redaphid/waveshare-round-stand/pocketwatch/renders/back-inside.png

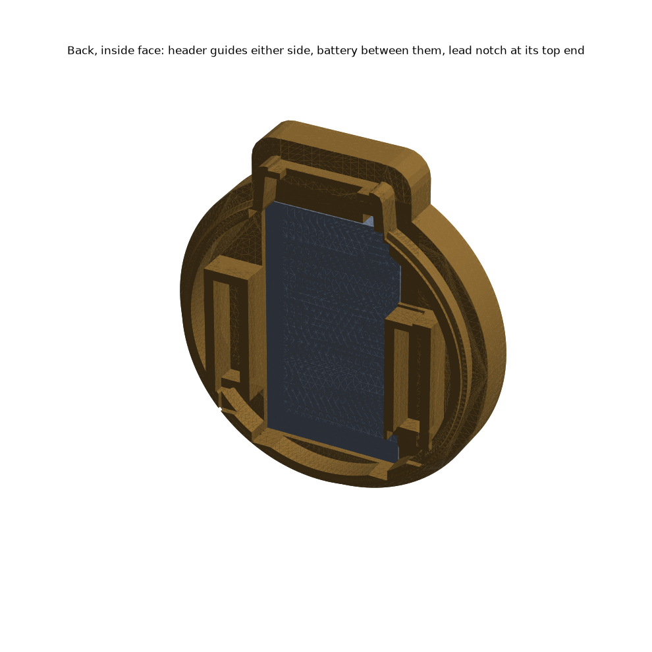
pocketwatch/renders/back-inside.png
