redaphid/waveshare-round-stand/pocketwatch/renders/front.png

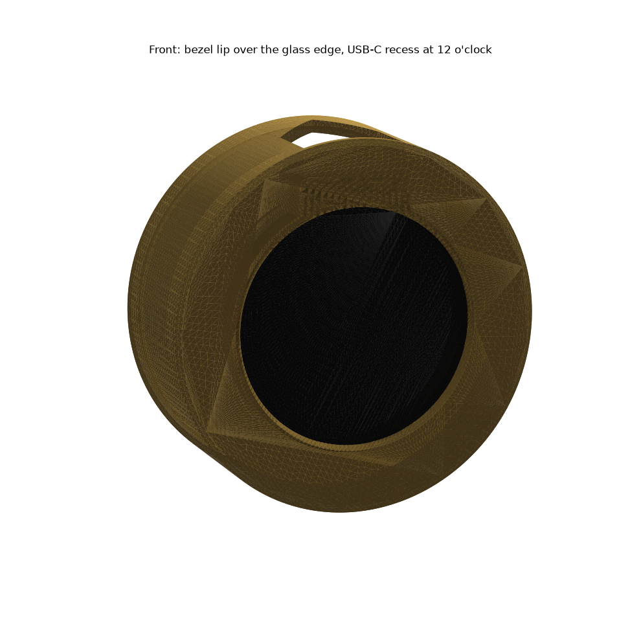
pocketwatch/renders/front.png
