redaphid/waveshare-round-stand/pocketwatch/renders/plate-front.png

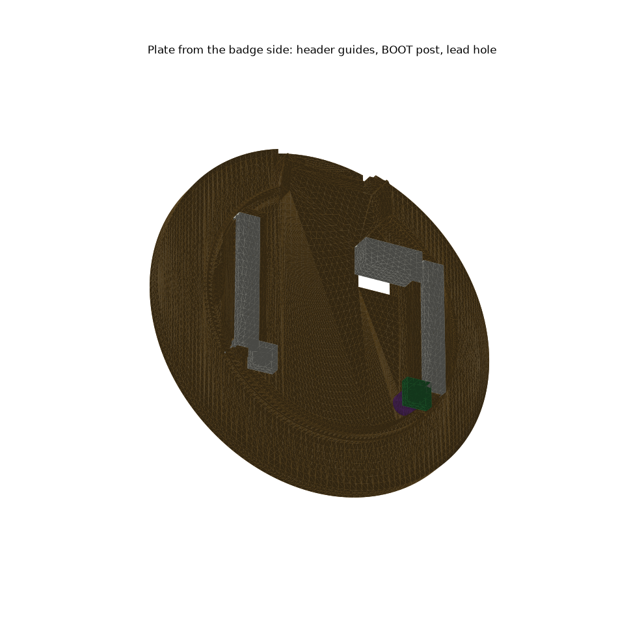
pocketwatch/renders/plate-front.png
