redaphid/waveshare-round-stand/pocketwatch/renders/section-post-detail-pressed.png

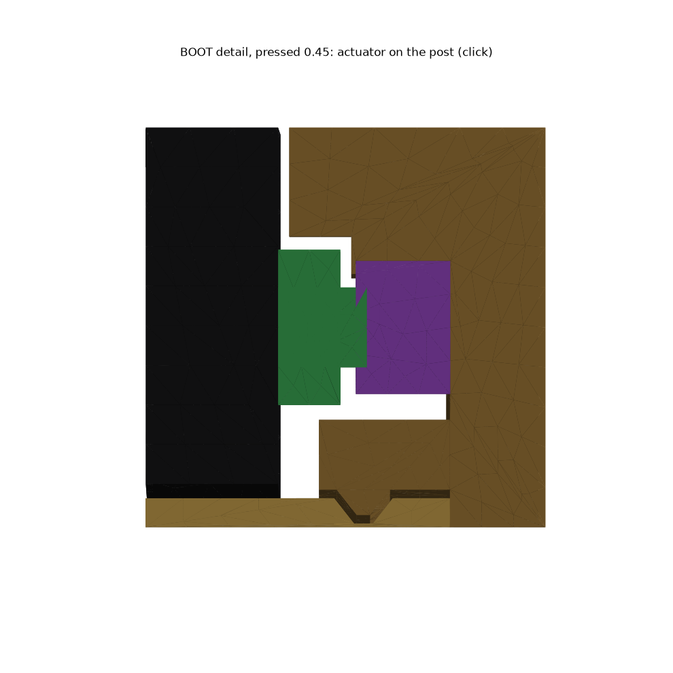
pocketwatch/renders/section-post-detail-pressed.png
