redaphid/waveshare-round-stand/pocketwatch/renders/section-post-detail-rest.png

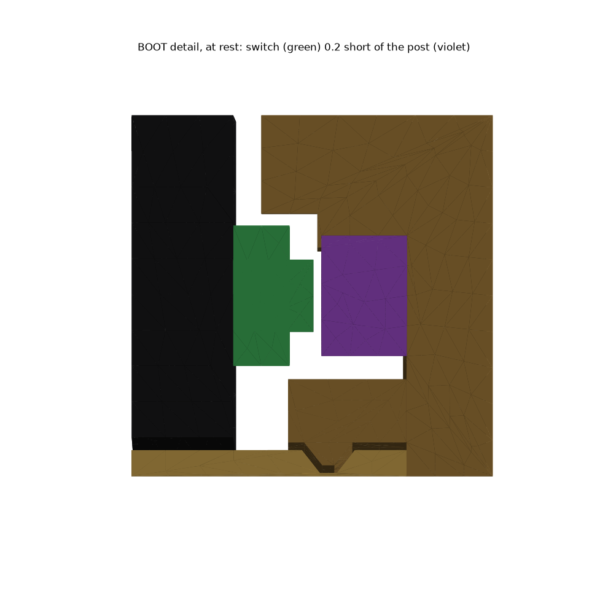
pocketwatch/renders/section-post-detail-rest.png
