redaphid/waveshare-round-stand/reference/esp32-s3-lcd-1.28-outline.jpg

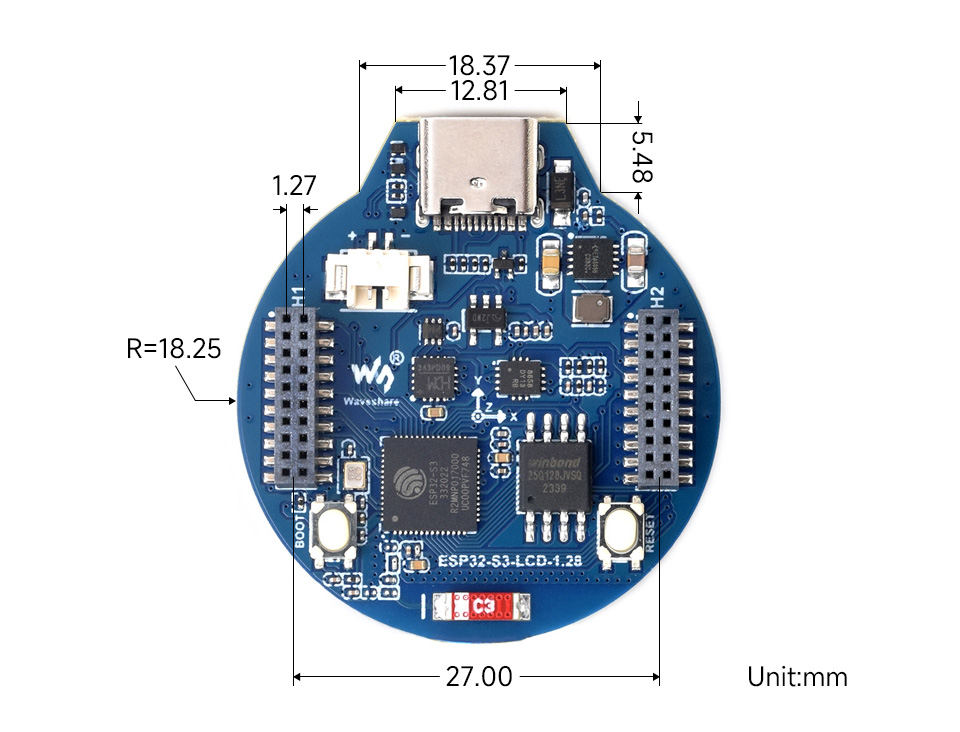
reference/esp32-s3-lcd-1.28-outline.jpg
