redaphid/waveshare-round-stand/reference/esp32-s3-lcd-1.28-switch-positions-photo.png

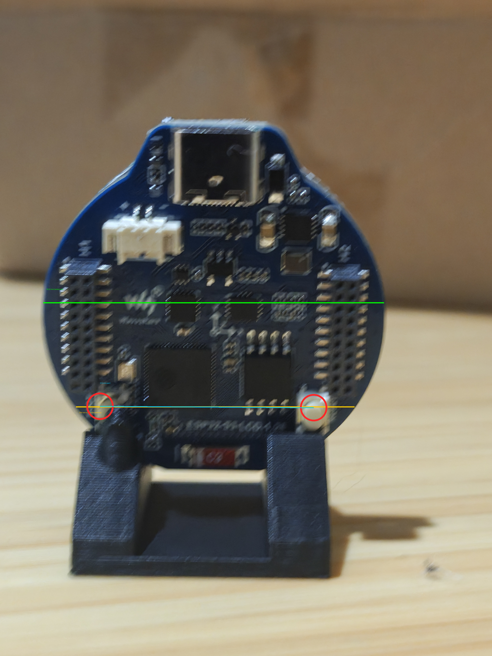
reference/esp32-s3-lcd-1.28-switch-positions-photo.png
