redaphid/waveshare-round-stand/reference/esp32-s3-touch-lcd-1.46-outline-bare.jpg

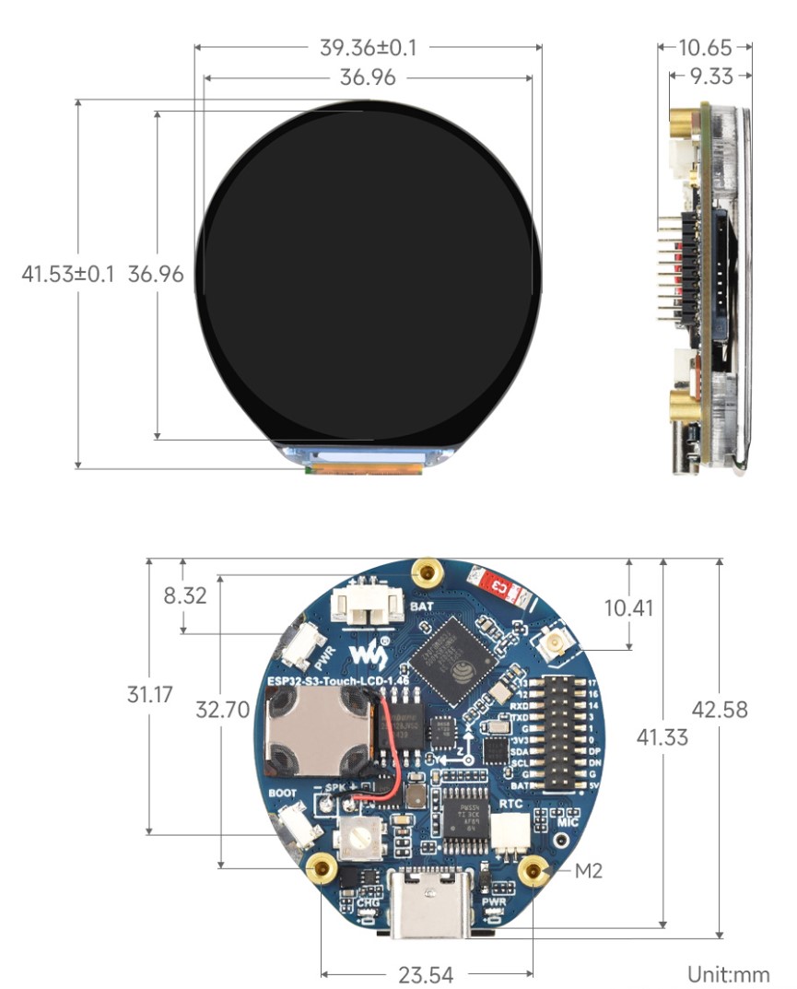
reference/esp32-s3-touch-lcd-1.46-outline-bare.jpg
