redaphid/waveshare-round-stand/renders/cup-stand-1.28-empty-front.png

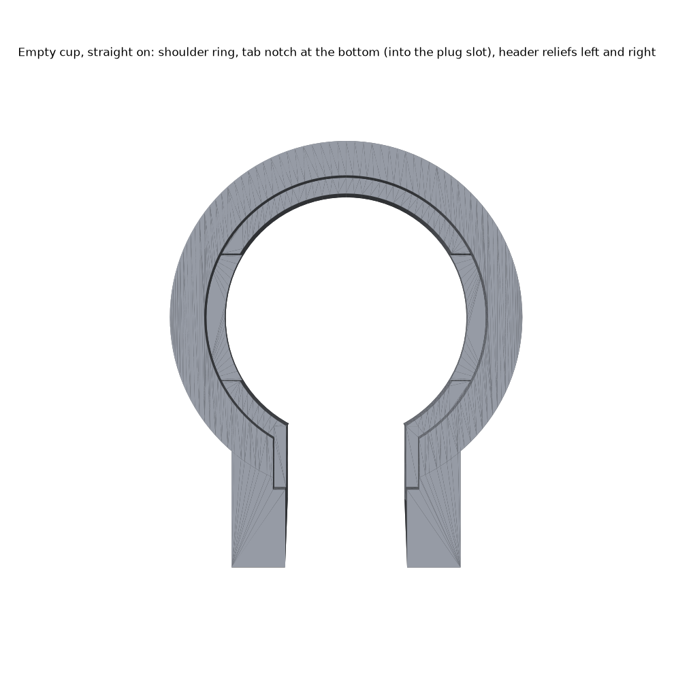
renders/cup-stand-1.28-empty-front.png
