redaphid/waveshare-round-stand/renders/fit-gauge.png

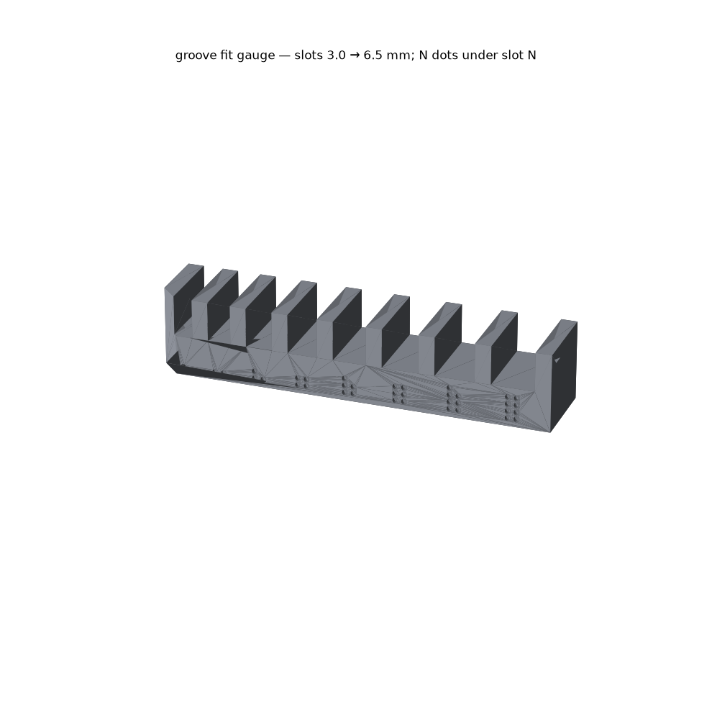
renders/fit-gauge.png
