redaphid/waveshare-round-stand/renders/stand-1.28-BOOT-post-front.png

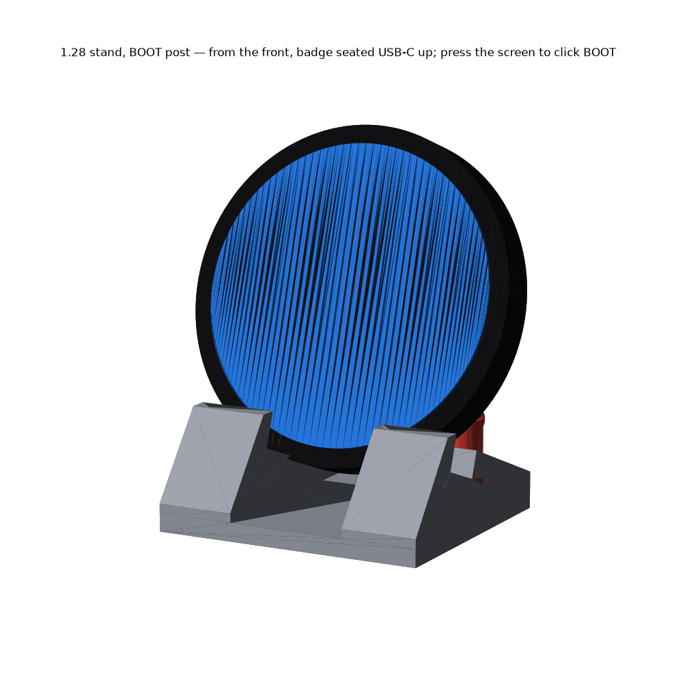
renders/stand-1.28-BOOT-post-front.png
