redaphid/waveshare-round-stand/renders/stand-1.28-usbdown-back.png

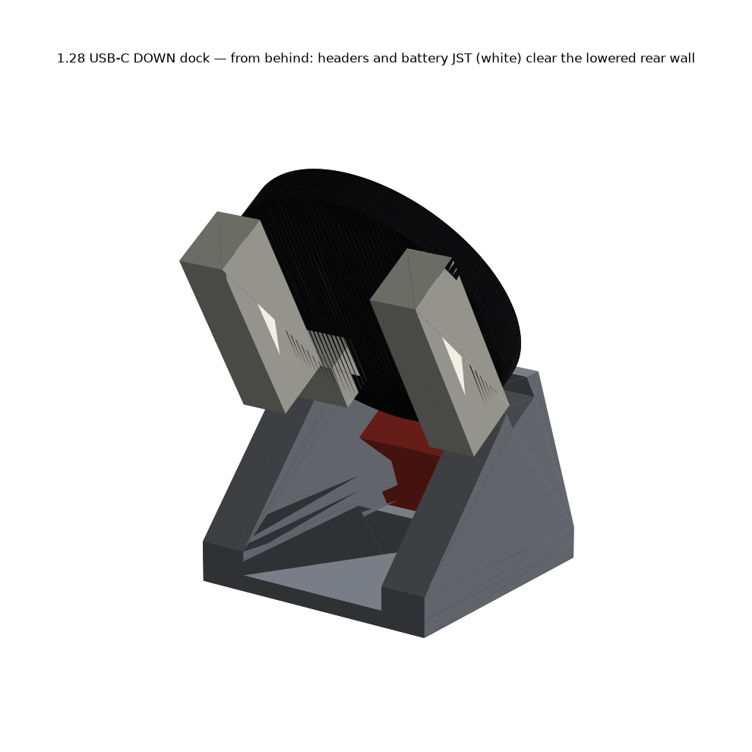
renders/stand-1.28-usbdown-back.png
