redaphid/waveshare-round-stand/renders/stand-1.28-usbdown-side.png

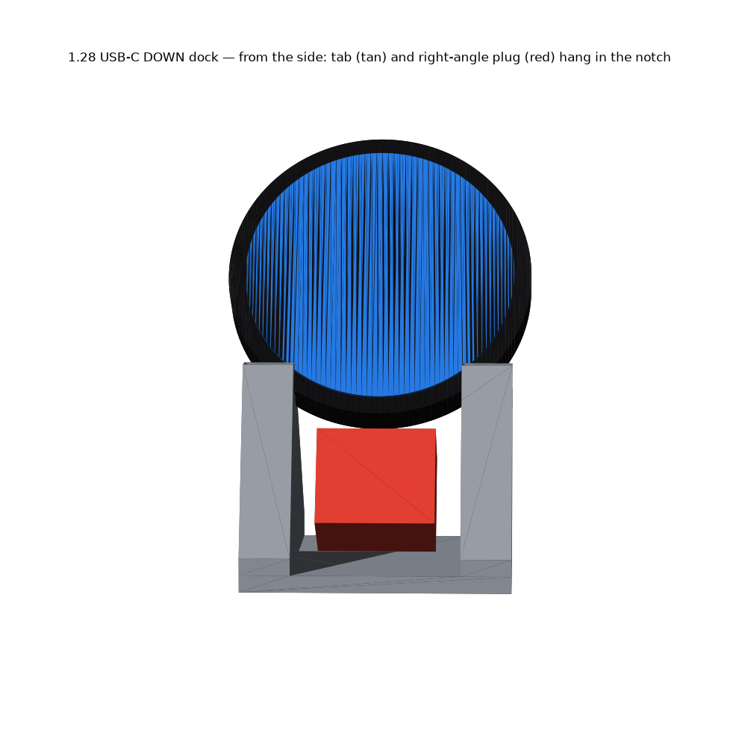
renders/stand-1.28-usbdown-side.png
