redaphid/waveshare-round-stand/stl/pod/Clip - slider.stl

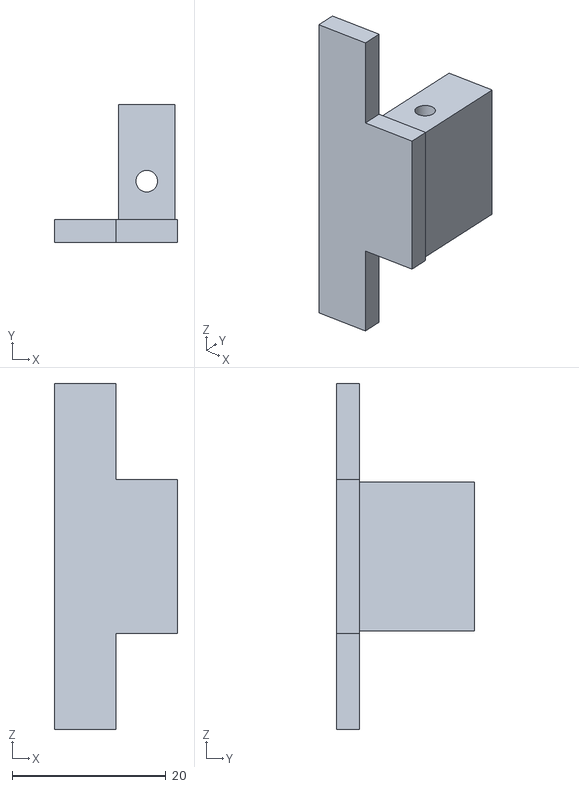
[picture p42: CAD file, 2026-09-18]
stl/pod/Clip - slider.stl
16.0 x 18.0 x 45.0
