redaphid/waveshare-round-stand/stl/large/Stand - no cover glass.stl

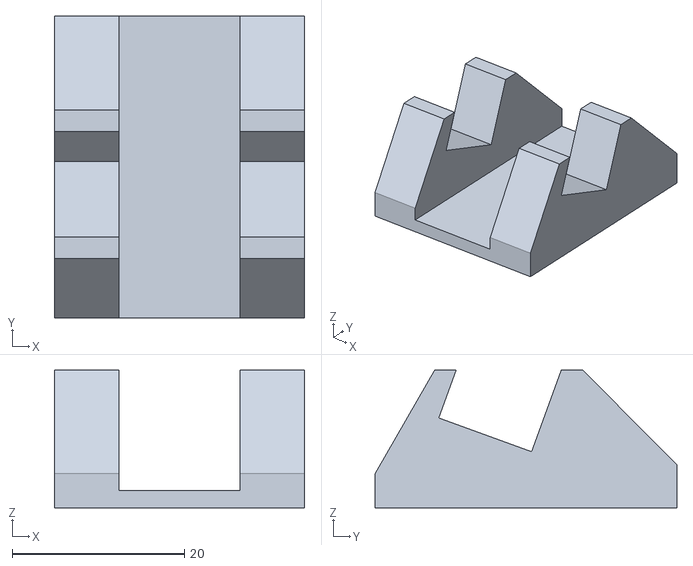
[picture p43: CAD file, 2026-09-18]
stl/large/Stand - no cover glass.stl
29.0 x 35.0 x 16.0
