redaphid/waveshare-round-stand/stl/small/Pod cup test.stl

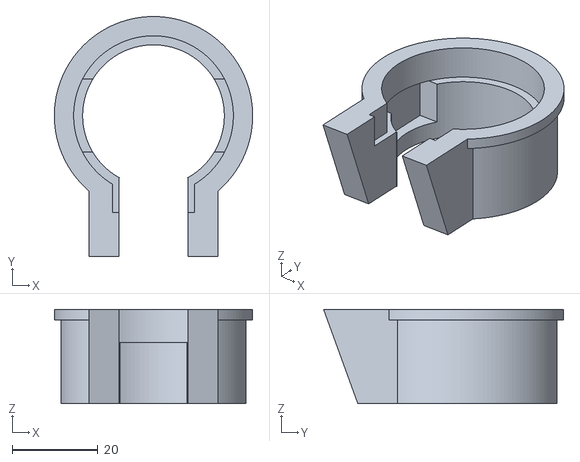
[picture p44: CAD file, 2026-09-19]
stl/small/Pod cup test.stl
46.2 x 55.9 x 22.0
