redaphid/waveshare-round-stand/stl/small/Slot fit gauge.stl

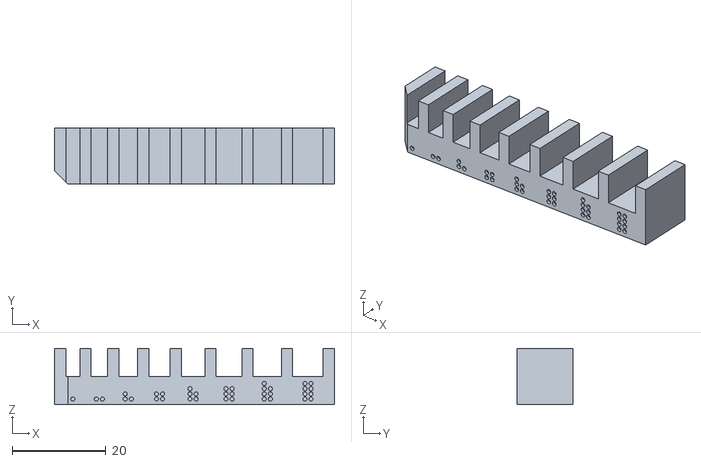
[picture p45: CAD file, 2026-09-19]
stl/small/Slot fit gauge.stl
59.6 x 12.0 x 12.0
