redaphid/waveshare-round-stand/stl/small/Trim ring - small.stl

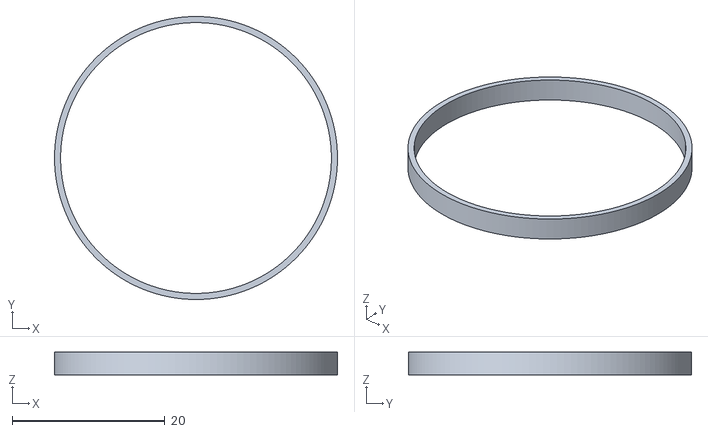
[picture p46: CAD file, 2026-09-18]
stl/small/Trim ring - small.stl
37.0 x 37.0 x 3.00
